kalinchuk/mark_8_reproduction/ram_rom_board/Schematics/Mark8RomRam_3.pdf

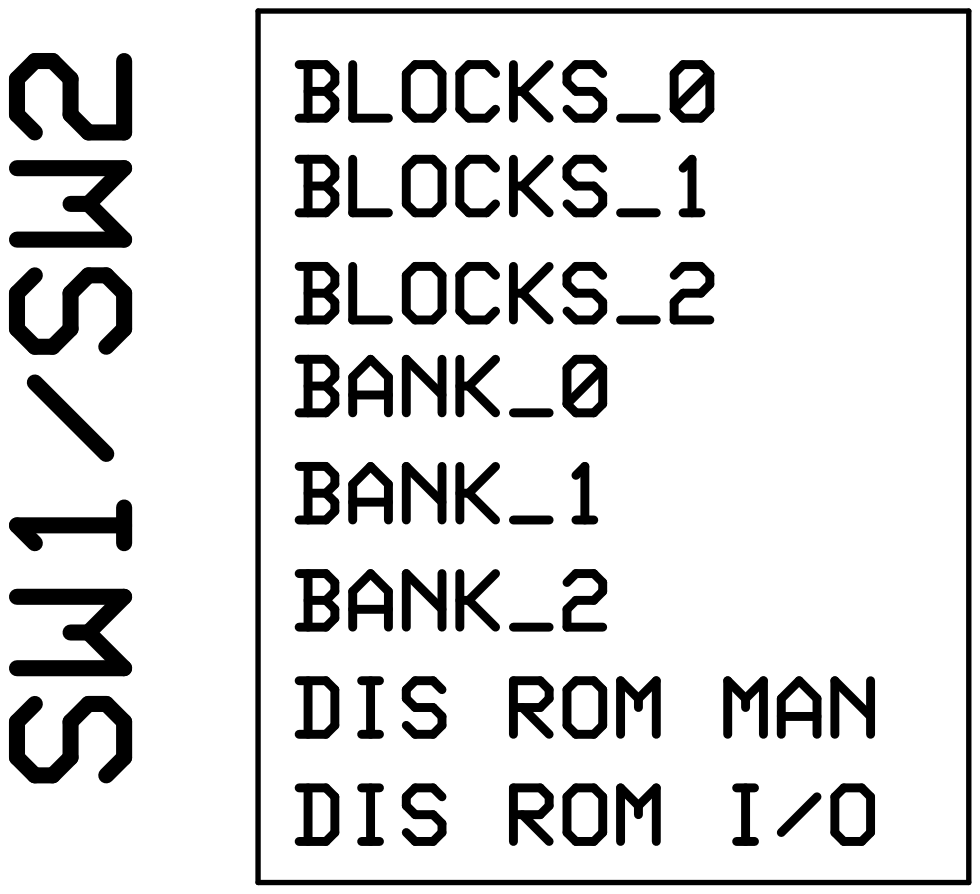
[picture p20: page 1]
